RandyPatterson/marqueeSign/src/annimation.h

#ifndef annimation_h
#define annimation_h

#include <Arduino.h>
#include <AnimatedGIF.h>
#include <WebServer.h>

class Annimation {
    public:
        static void init(MatrixPanel_I2S_DMA *dma_display, WebServer *webserver);
        static void ShowGIF(char *name);
    private: 
        static void GIFDrawFile(GIFDRAW *pDraw);
        static void * GIFOpenFile(const char *fname, int32_t *pSize);
        static int32_t GIFReadFile(GIFFILE *pFile, uint8_t *pBuf, int32_t iLen);
        static void GIFCloseFile(void *pHandle);
        static int32_t GIFSeekFile(GIFFILE *pFile, int32_t iPosition);
        static MatrixPanel_I2S_DMA *_dma_display;
        static AnimatedGIF _gif;
        static File _f;
        static int x_offset;
        static int y_offset;
        static WebServer *_webserver;
};

#endif
